TseYatSing/Tse-Arm/Model/G/G.SLDASM

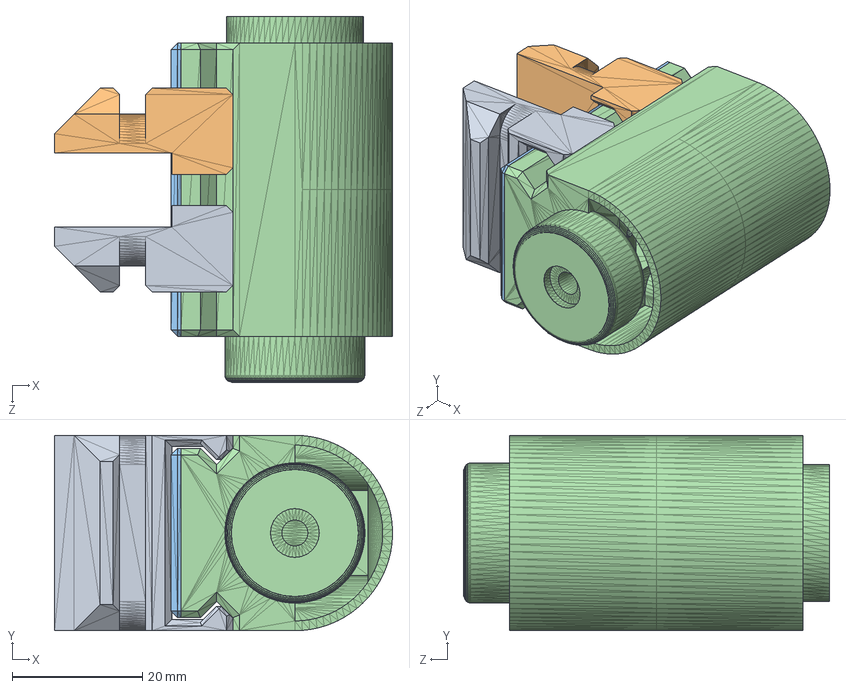
[picture p6: CAD file, 2025-01-12]
Model/G/G.SLDASM
51.9 x 30.0 x 56.2 mm
G1
G2
G3
G4
