TseYatSing/Tse-Arm/Model/URDF/robot arm.SLDASM/meshes/S_Link.STL

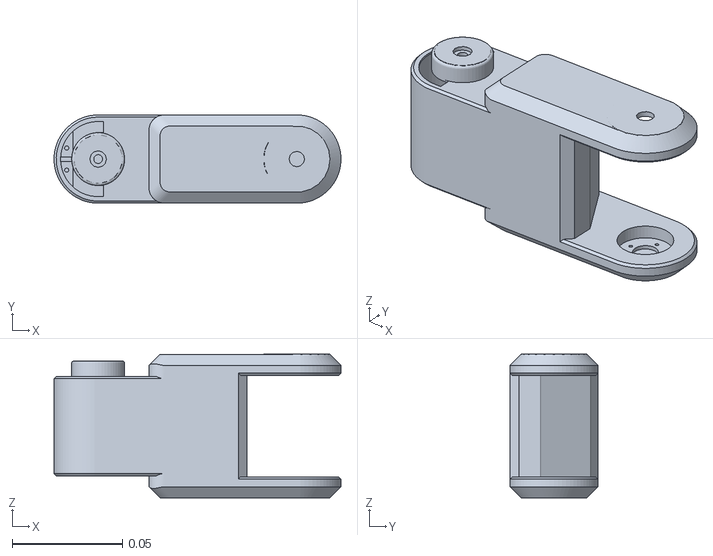
[picture p19: CAD file, 2025-01-12]
Model/URDF/robot arm.SLDASM/meshes/S_Link.STL
0.13 x 0.0399 x 0.0651
