TseYatSing/Tse-Arm/Model/F/F2C.SLDPRT

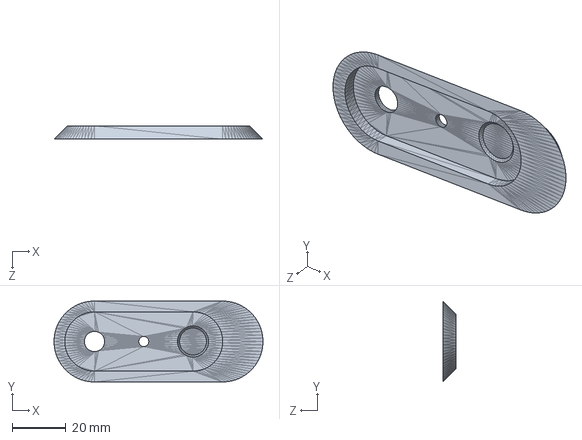
[picture p20: CAD file, 2025-01-12]
Model/F/F2C.SLDPRT
77.4 x 30.0 x 5.00 mm
