TseYatSing/Tse-Arm/Model/G/G4.SLDPRT

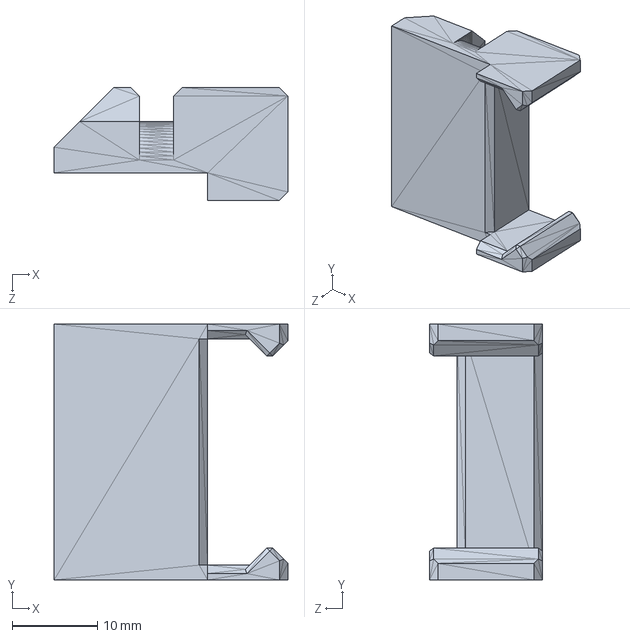
[picture p21: CAD file, 2025-01-12]
Model/G/G4.SLDPRT
27.4 x 30.0 x 13.2 mm
