TseYatSing/Tse-Arm/Model/MB/MB3.SLDPRT

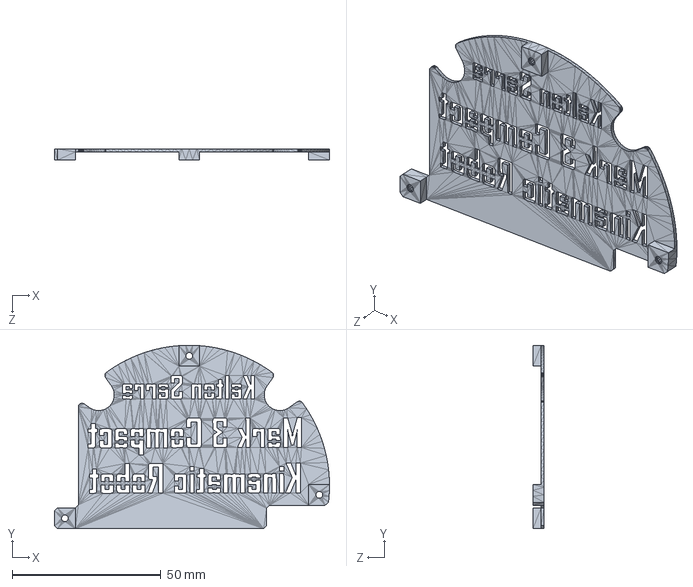
[picture p22: CAD file, 2025-01-12]
Model/MB/MB3.SLDPRT
92.4 x 61.6 x 3.75 mm
