TseYatSing/Tse-Arm/Model/URDF/robot arm.SLDASM/meshes/base_link.STL

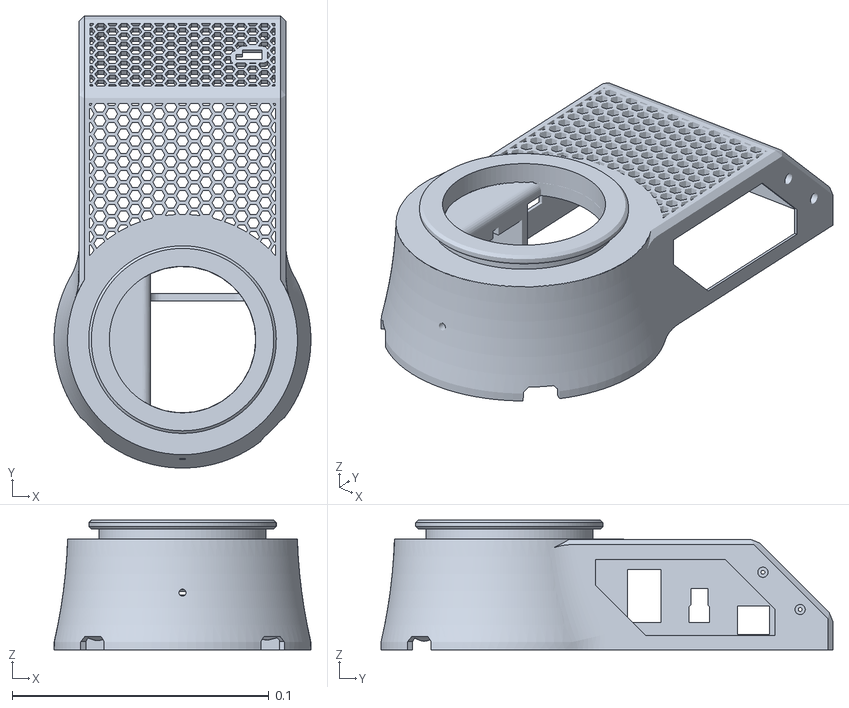
[picture p23: CAD file, 2025-01-12]
Model/URDF/robot arm.SLDASM/meshes/base_link.STL
0.1 x 0.176 x 0.0505
