TseYatSing/Tse-Arm/Model/G/G1.SLDPRT

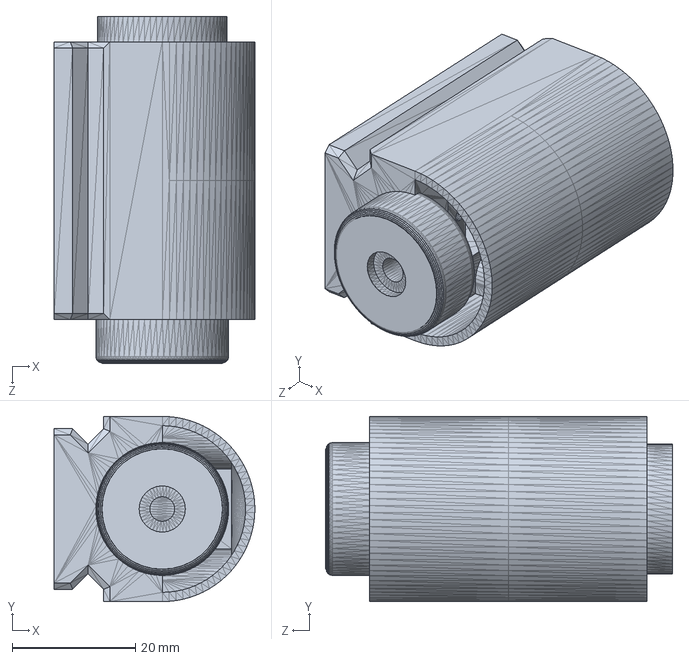
[picture p24: CAD file, 2025-01-12]
Model/G/G1.SLDPRT
32.5 x 30.0 x 56.2 mm
