TseYatSing/Tse-Arm/Model/URDF/robot arm.SLDASM/meshes/E_Link.STL

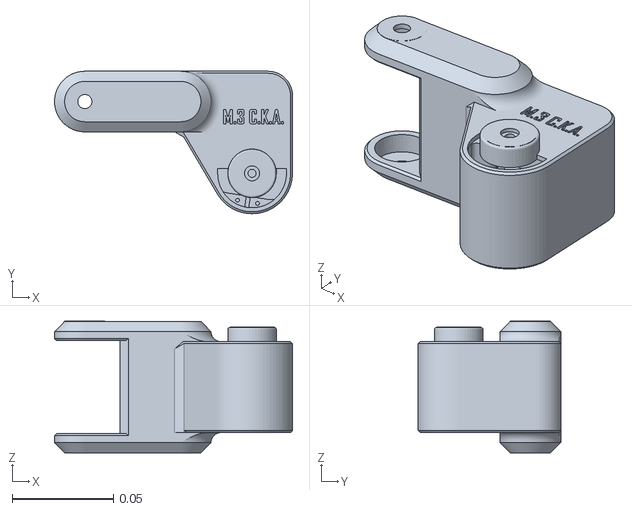
[picture p25: CAD file, 2025-01-12]
Model/URDF/robot arm.SLDASM/meshes/E_Link.STL
0.118 x 0.0705 x 0.0651
