TseYatSing/Tse-Arm/Model/URDF/robot arm.SLDASM/meshes/W_Link.STL

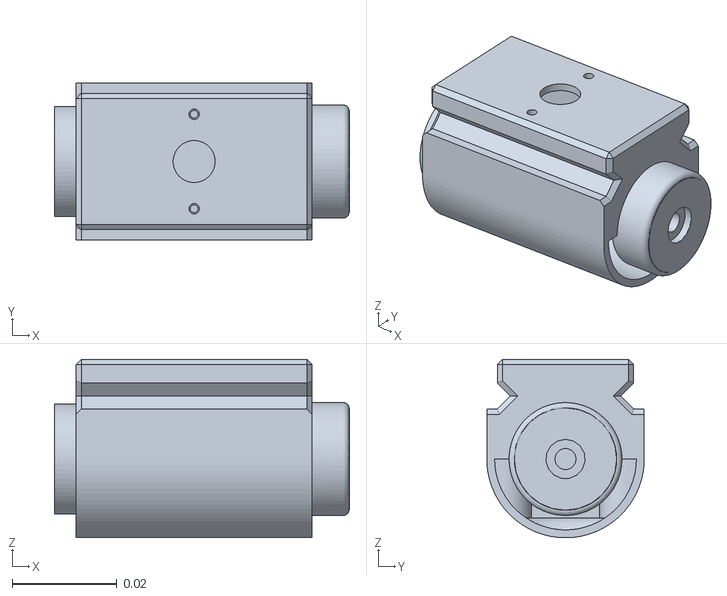
[picture p26: CAD file, 2025-01-12]
Model/URDF/robot arm.SLDASM/meshes/W_Link.STL
0.0562 x 0.03 x 0.034
