TseYatSing/Tse-Arm/Model/URDF/robot arm.SLDASM/meshes/HL_Link.STL

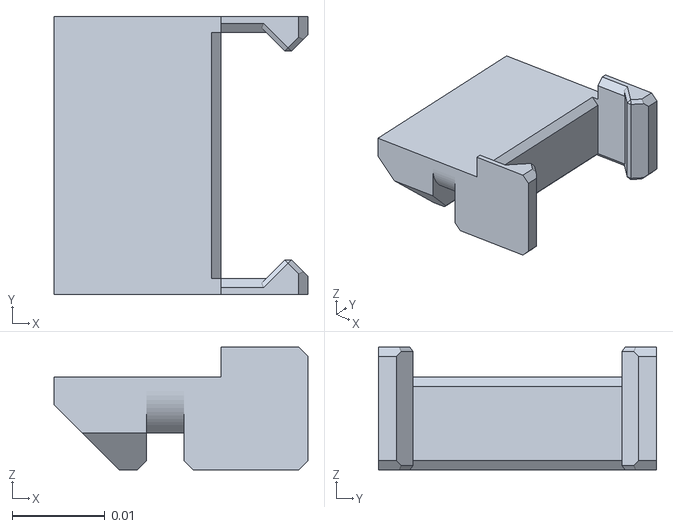
[picture p27: CAD file, 2025-01-12]
Model/URDF/robot arm.SLDASM/meshes/HL_Link.STL
0.0274 x 0.03 x 0.0132
