TseYatSing/Tse-Arm/Model/B/B (1).SLDASM

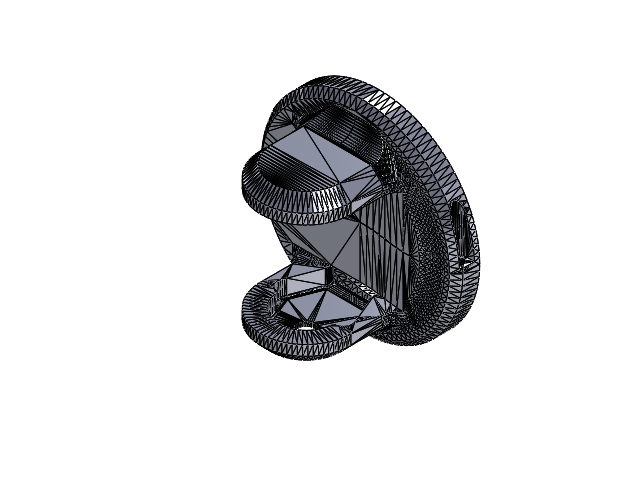
[picture p28: CAD file, 2025-01-12]
Model/B/B (1).SLDASM
B1
B2
